Klabbob/SEN66-IAQ-Monitor/SquareLine Studio Projects/Main Screens/cache/thumb_1190020983TempScreen.png

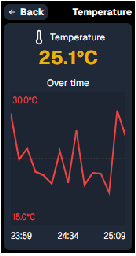
SquareLine Studio Projects/Main Screens/cache/thumb_1190020983TempScreen.png
