Klabbob/SEN66-IAQ-Monitor/SquareLine Studio Projects/Main Screens/cache/thumb_1267981470PMScreen.png

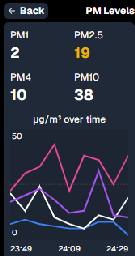
SquareLine Studio Projects/Main Screens/cache/thumb_1267981470PMScreen.png
