Klabbob/SEN66-IAQ-Monitor/SquareLine Studio Projects/Main Screens/cache/thumb_1843866084MainScreen.png

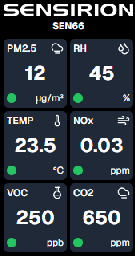
SquareLine Studio Projects/Main Screens/cache/thumb_1843866084MainScreen.png
